deniskokarev/vgame/soft/Inc/crc.h

/**
  ******************************************************************************
  * File Name          : CRC.h
  * Description        : This file provides code for the configuration
  *                      of the CRC instances.
  ******************************************************************************
  *
  * COPYRIGHT(c) 2016 STMicroelectronics
  *
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
  ******************************************************************************
  */
/* Define to prevent recursive inclusion -------------------------------------*/
#ifndef __crc_H
#define __crc_H
#ifdef __cplusplus
 extern "C" {
#endif

/* Includes ------------------------------------------------------------------*/
#include "stm32f3xx_hal.h"

extern CRC_HandleTypeDef hcrc;

void MX_CRC_Init(void);

#ifdef __cplusplus
}
#endif
#endif /*__ crc_H */

/**
  * @}
  */

/**
  * @}
  */

/************************ (C) COPYRIGHT STMicroelectronics *****END OF FILE****/
